nandfarm/PowerRiser/Photos/powerriser-lenovo-riser-m2-nvme-installed-gpu.jpg

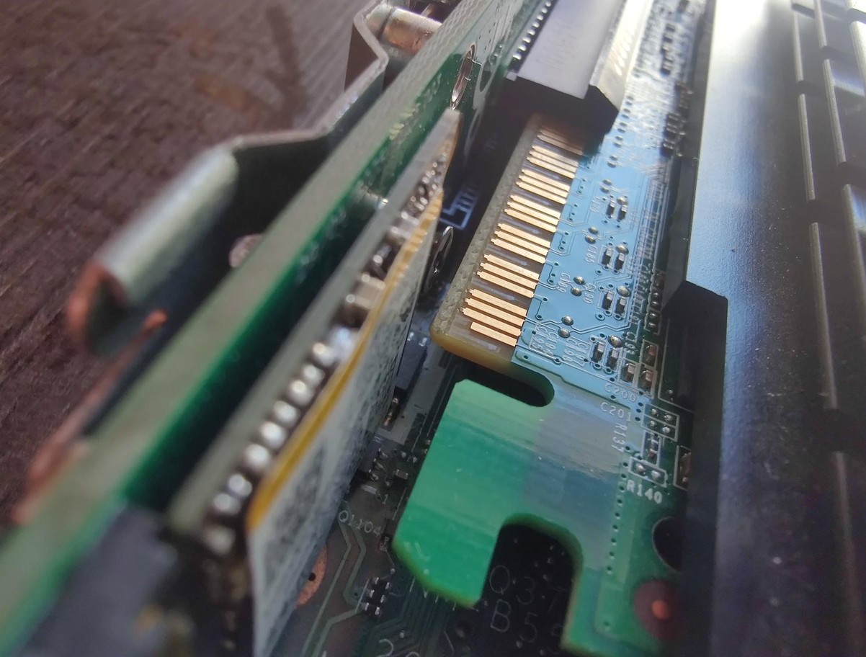
Photos/powerriser-lenovo-riser-m2-nvme-installed-gpu.jpg
