nandfarm/PowerRiser/Photos/powerriser-lenovo-riser-m2-nvme-installed-side-2.jpg

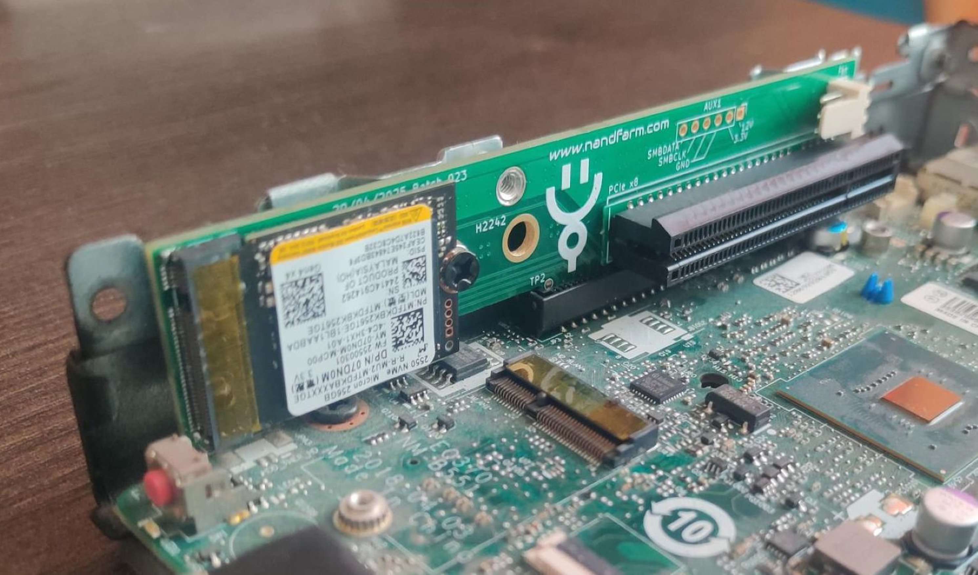
Photos/powerriser-lenovo-riser-m2-nvme-installed-side-2.jpg
