nandfarm/PowerRiser/Photos/powerriser-lenovo-riser-m2-nvme-side-ssd-installed.jpg

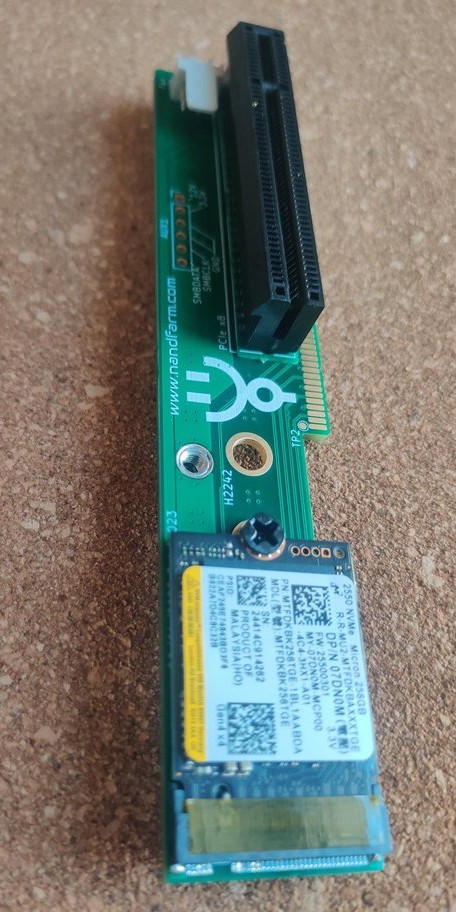
Photos/powerriser-lenovo-riser-m2-nvme-side-ssd-installed.jpg
